theRosyProject/PIONEER/docs/manual/esp8266/adafruit_products_Huzzah_ESP8266_Pinout_v1.2-1.png.pdf

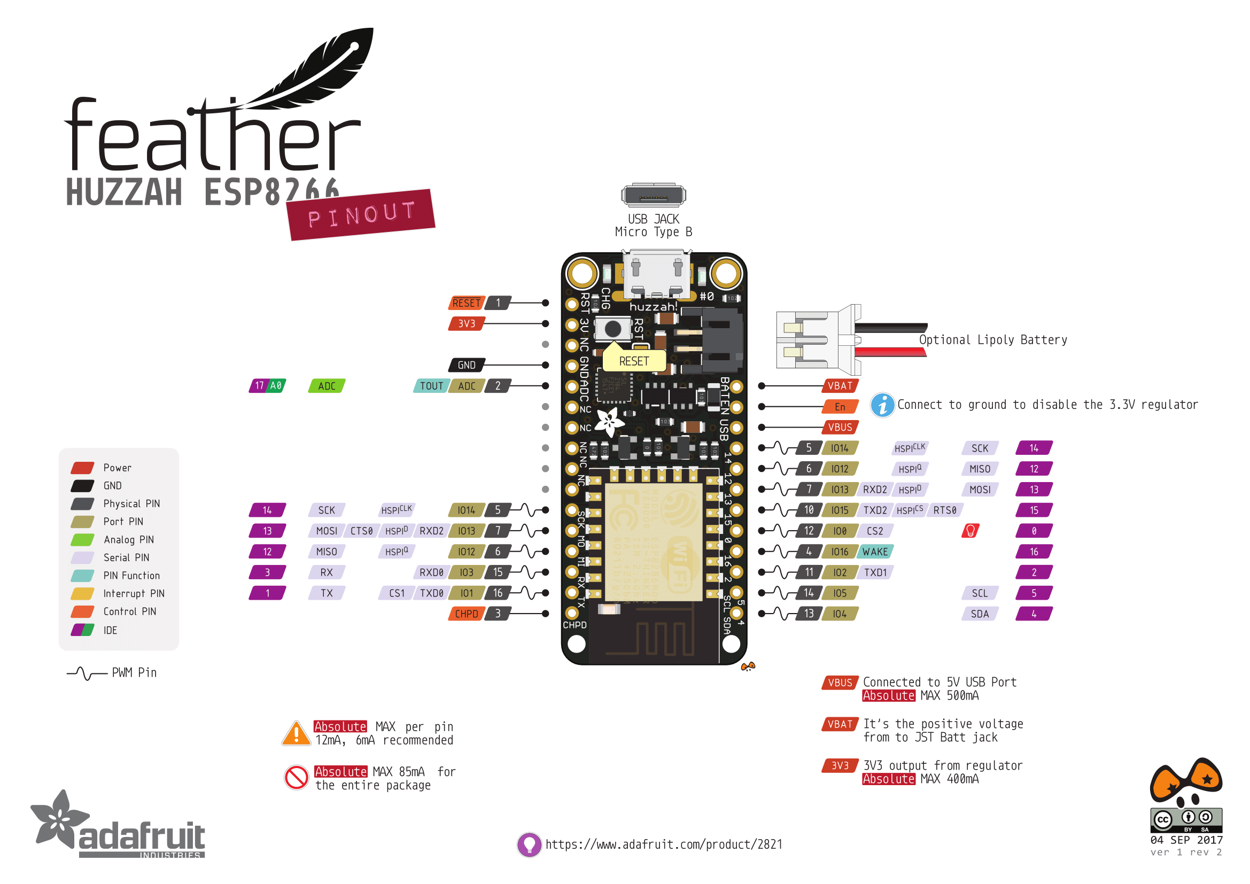
[picture p1: page 1]
