theRosyProject/PIONEER/docs/admin/meetings/2023-04-20/Screenshot 2023-04-20 at 15.48.45.png

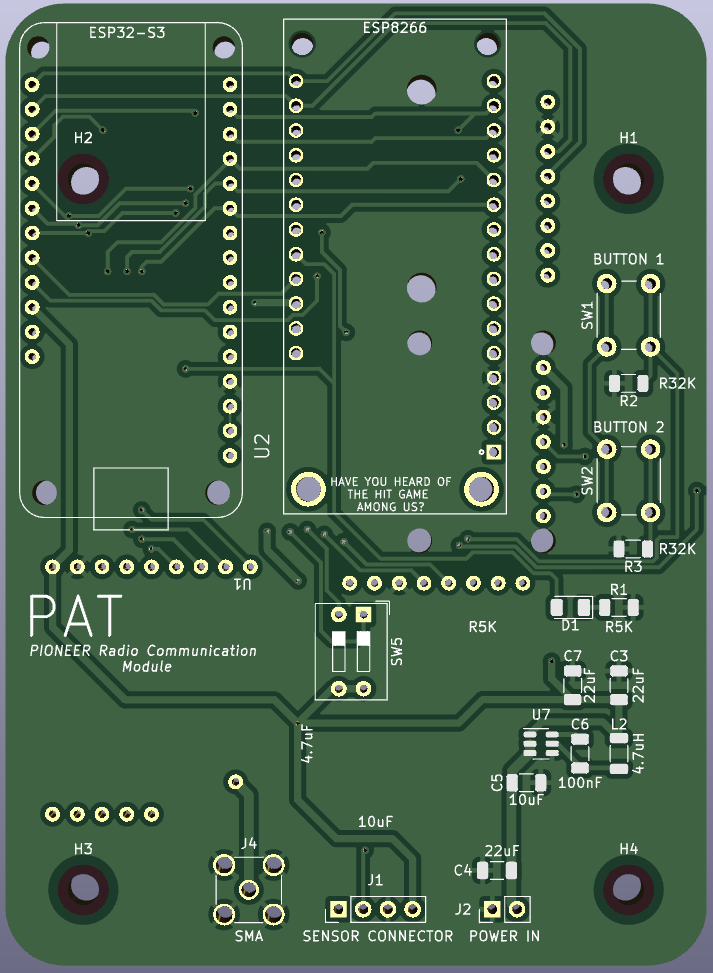
docs/admin/meetings/2023-04-20/Screenshot 2023-04-20 at 15.48.45.png
