theRosyProject/PIONEER/hardware/Sensor Box/Sensors/NDIR Transmitter.SLDPRT

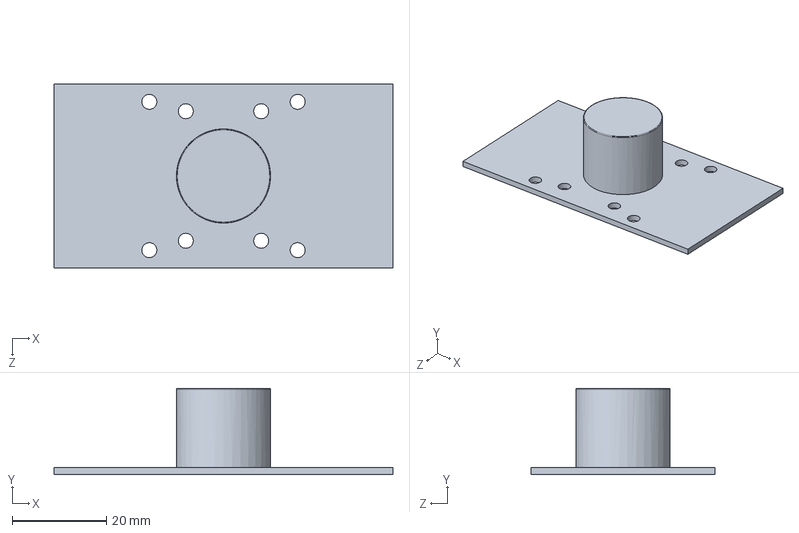
[picture p21: CAD file, 2023-03-03]
hardware/Sensor Box/Sensors/NDIR Transmitter.SLDPRT
72.0 x 18.3 x 39.0 mm
