theRosyProject/PIONEER/hardware/Controller Box/Box/Box_Lid.SLDPRT

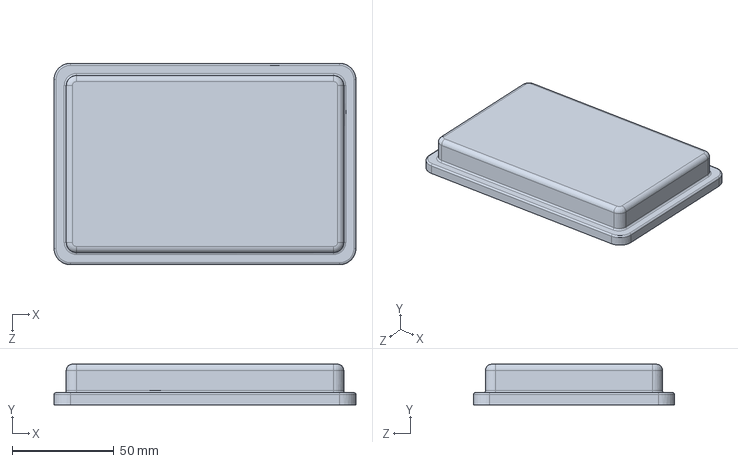
[picture p22: CAD file, 2022-10-02]
hardware/Controller Box/Box/Box_Lid.SLDPRT
148.5 x 20.0 x 99.0 mm
