theRosyProject/PIONEER/hardware/Controller Box/PCB Models/PCB_Board.SLDPRT

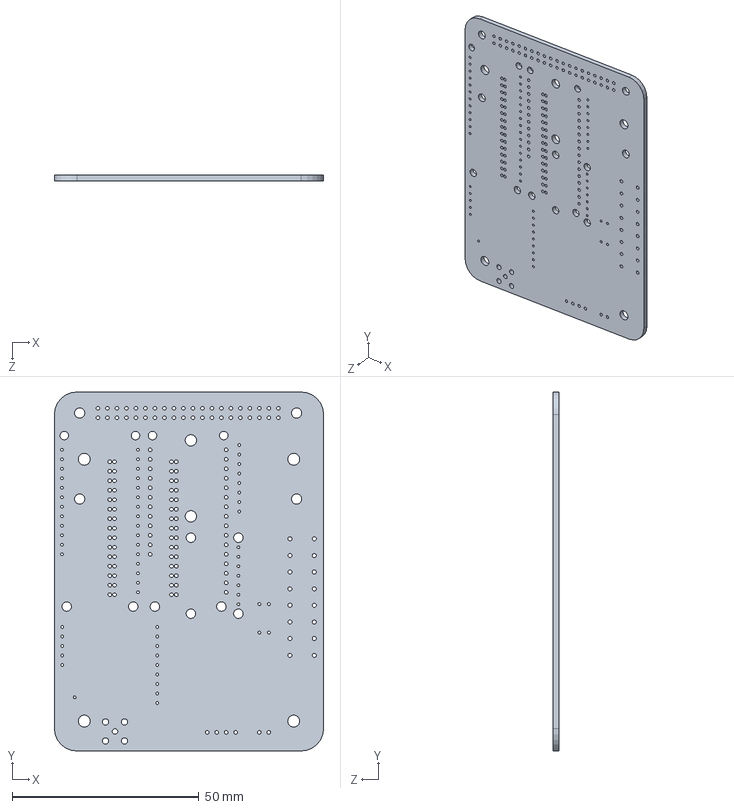
[picture p24: CAD file, 2022-10-10]
hardware/Controller Box/PCB Models/PCB_Board.SLDPRT
72.0 x 96.0 x 1.60 mm
