theRosyProject/PIONEER/hardware/Controller Box/PCB Models/stp/SW-NDS-02V.stp

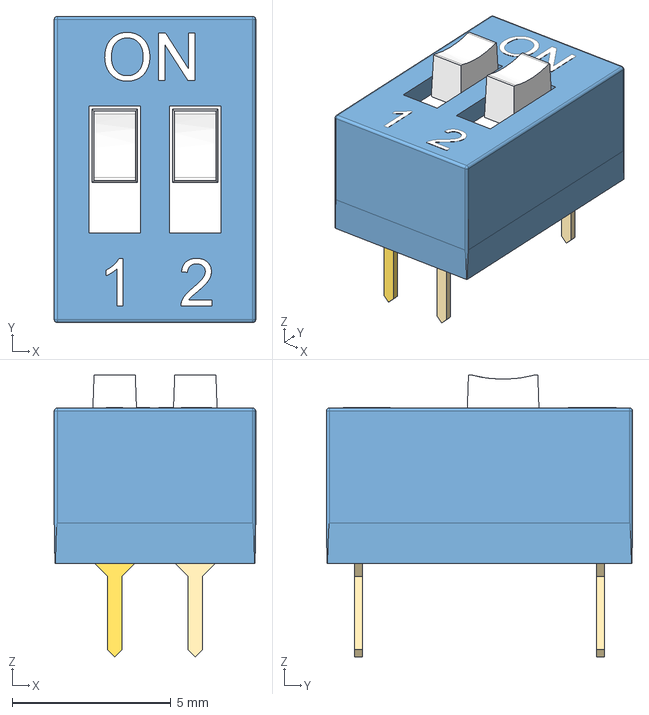
[picture p25: CAD file, 2022-10-10]
hardware/Controller Box/PCB Models/stp/SW-NDS-02V.stp
6.35 x 9.65 x 8.88 mm
