theRosyProject/PIONEER/hardware/Controller Box/PCB_Simplified.SLDPRT

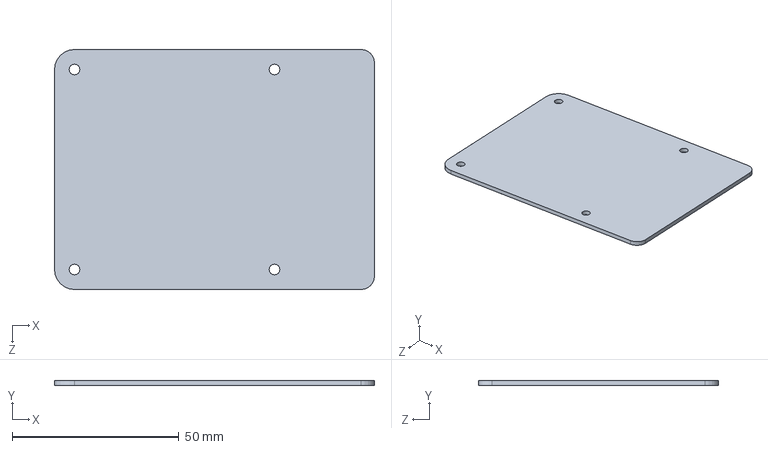
[picture p26: CAD file, 2022-10-02]
hardware/Controller Box/PCB_Simplified.SLDPRT
96.0 x 1.60 x 72.0 mm
