theRosyProject/PIONEER/hardware/Sensor Box/Sensors/PMS5003.SLDPRT

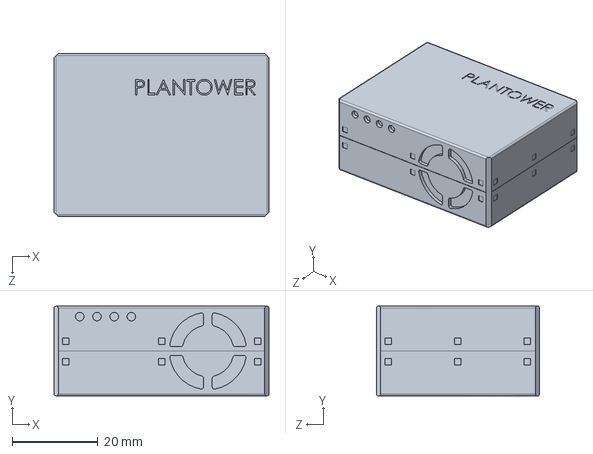
[picture p27: CAD file, 2022-11-28]
hardware/Sensor Box/Sensors/PMS5003.SLDPRT
50.0 x 20.9 x 38.0 mm
