theRosyProject/PIONEER/hardware/Controller Box/Connectors/Connector Cnlinko LP-12 2 poles.STEP

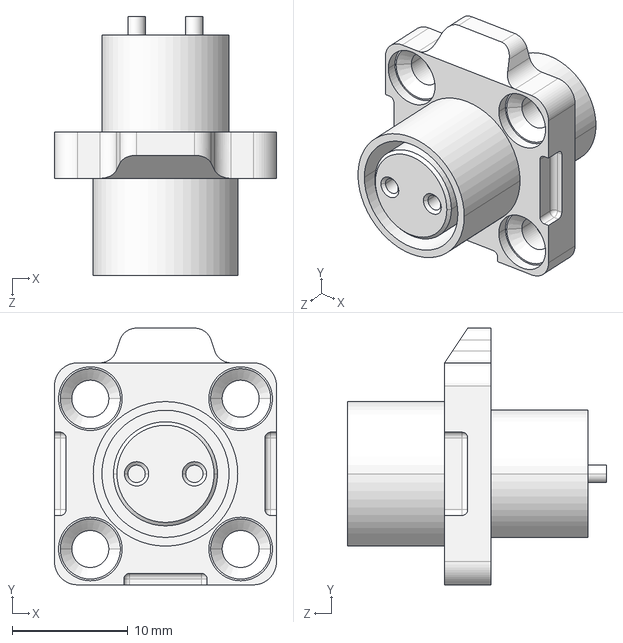
[picture p28: CAD file, 2022-10-08]
hardware/Controller Box/Connectors/Connector Cnlinko LP-12 2 poles.STEP
19.2 x 22.2 x 22.4 mm
