theRosyProject/PIONEER/hardware/Controller Box/PCB Models/stp/SW-NDS-08V.stp

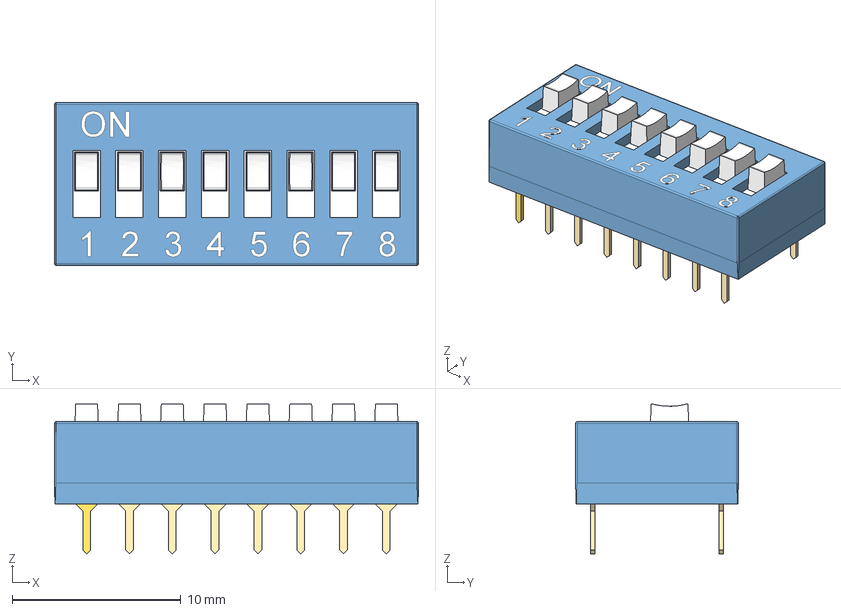
[picture p30: CAD file, 2022-10-10]
hardware/Controller Box/PCB Models/stp/SW-NDS-08V.stp
21.6 x 9.65 x 8.88 mm
