theRosyProject/PIONEER/hardware/Sensor Box/Sensors/Alphsense_Gas_Sensor.SLDPRT

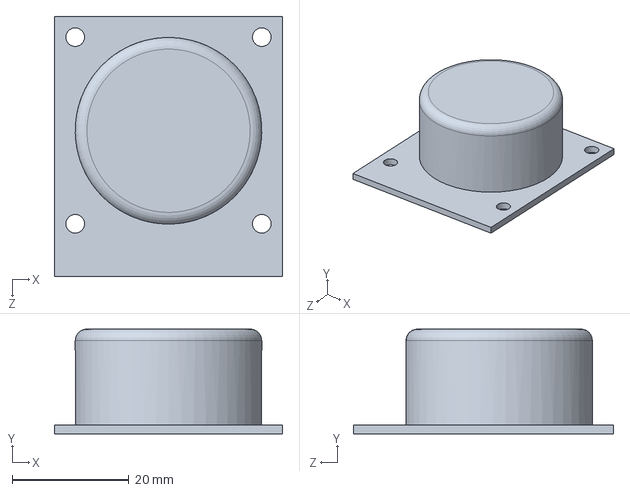
[picture p31: CAD file, 2022-11-28]
hardware/Sensor Box/Sensors/Alphsense_Gas_Sensor.SLDPRT
39.1 x 18.0 x 44.6 mm
