theRosyProject/PIONEER/hardware/Controller Box/PCB Models/stp/SW-NDS-04V.stp

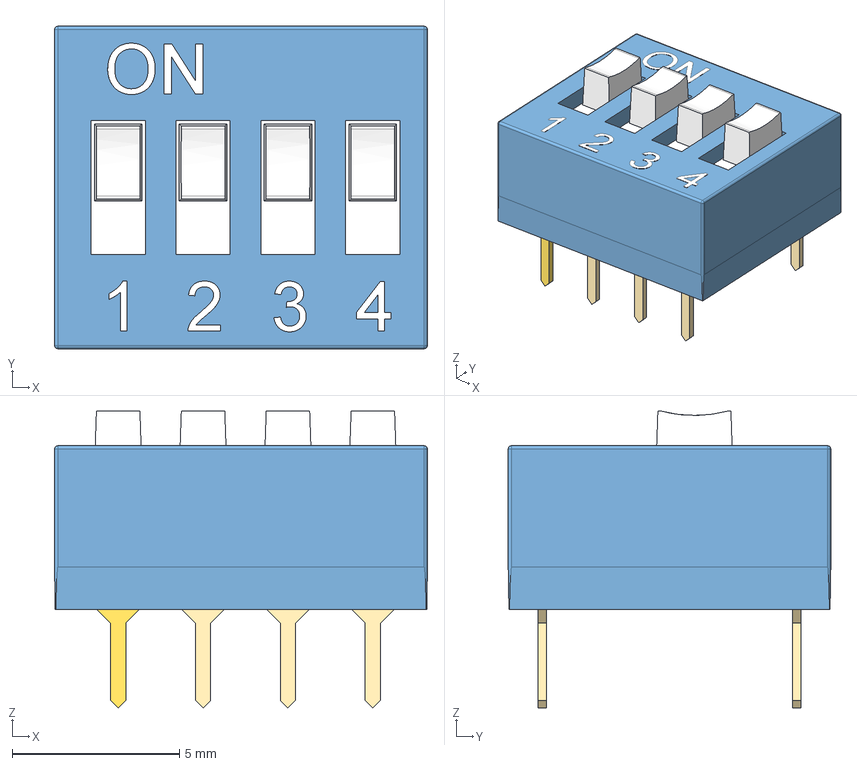
[picture p33: CAD file, 2022-10-10]
hardware/Controller Box/PCB Models/stp/SW-NDS-04V.stp
11.2 x 9.65 x 8.88 mm
