theRosyProject/PIONEER/hardware/STL Files/top_frame.STL

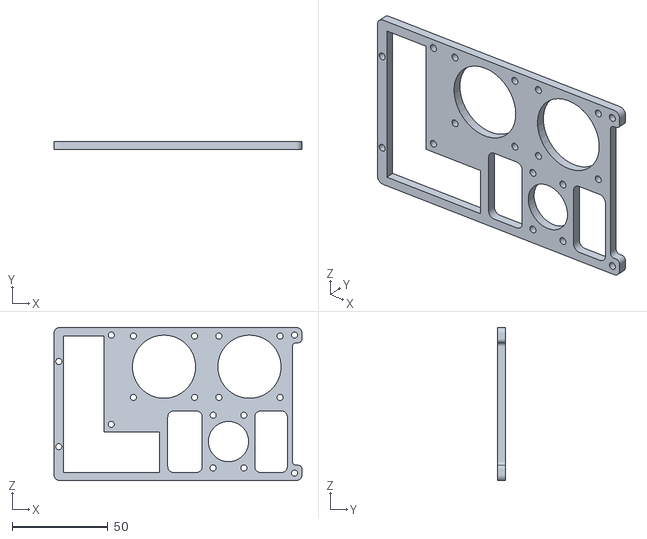
[picture p34: CAD file, 2023-03-03]
hardware/STL Files/top_frame.STL
129.4 x 4.00 x 79.9
