theRosyProject/PIONEER/hardware/Controller Box/PCB Models/stp/SW-NDS-06V.stp

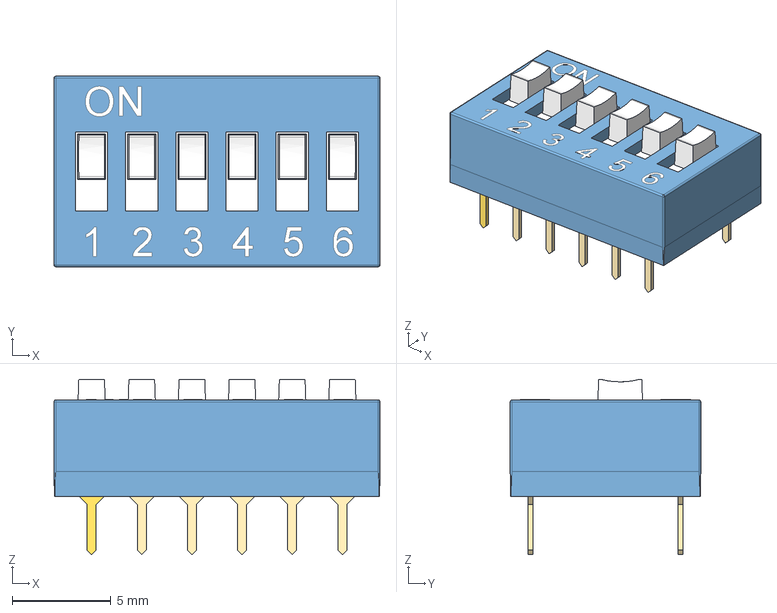
[picture p36: CAD file, 2022-10-10]
hardware/Controller Box/PCB Models/stp/SW-NDS-06V.stp
16.5 x 9.65 x 8.88 mm
