theRosyProject/PIONEER/hardware/Controller Box/PCB Models/Tactal Switch - SMD (12mmx12mmx5.5mm).stp

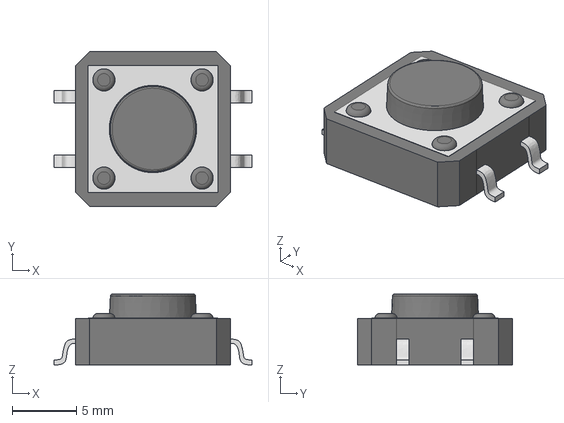
[picture p37: CAD file, 2022-10-08]
hardware/Controller Box/PCB Models/Tactal Switch - SMD (12mmx12mmx5.5mm).stp
15.4 x 12.0 x 5.50 mm
