theRosyProject/PIONEER/hardware/Controller Box/PCB Models/stp/SW-NDS-07V.stp

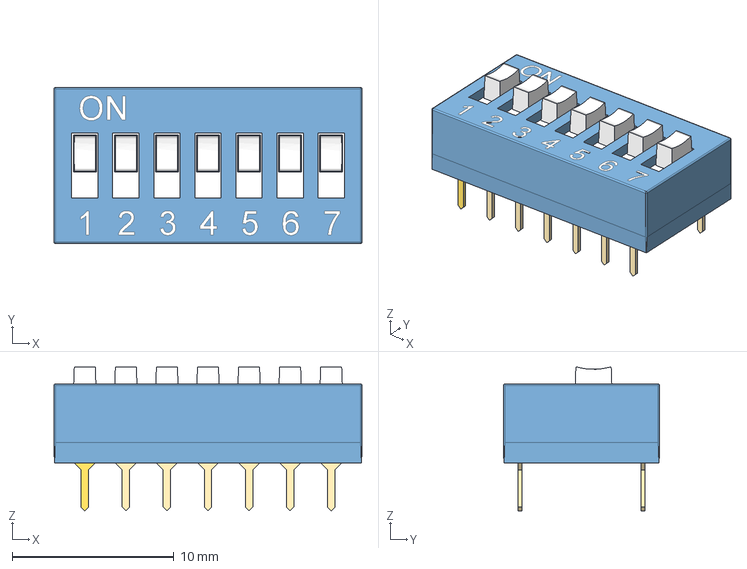
[picture p39: CAD file, 2022-10-10]
hardware/Controller Box/PCB Models/stp/SW-NDS-07V.stp
19.1 x 9.65 x 8.88 mm
