theRosyProject/PIONEER/hardware/Controller Box/PCB Models/Tactal Switch -Thru (6mmx 6mmx4.5mm).stp

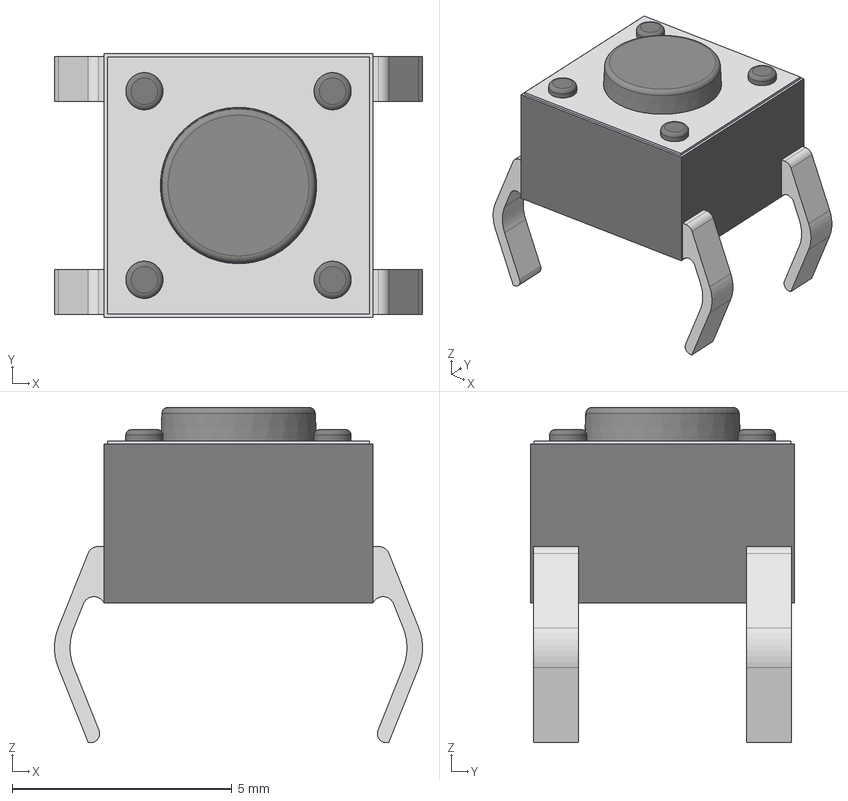
[picture p40: CAD file, 2022-10-08]
hardware/Controller Box/PCB Models/Tactal Switch -Thru (6mmx 6mmx4.5mm).stp
8.37 x 5.99 x 7.62 mm
