theRosyProject/PIONEER/hardware/Sensor Box/Sensor_PCB.SLDPRT

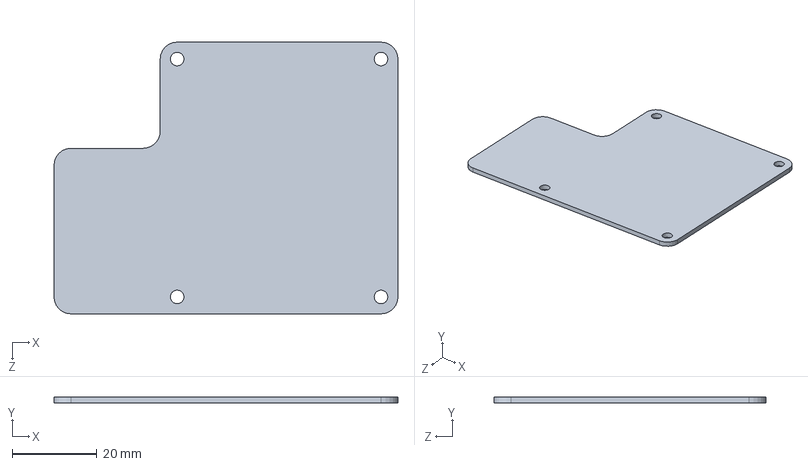
[picture p41: CAD file, 2023-01-13]
hardware/Sensor Box/Sensor_PCB.SLDPRT
81.0 x 1.50 x 64.0 mm
