theRosyProject/PIONEER/hardware/Controller Box/PCB Models/stp/SW-NDS-03V.stp

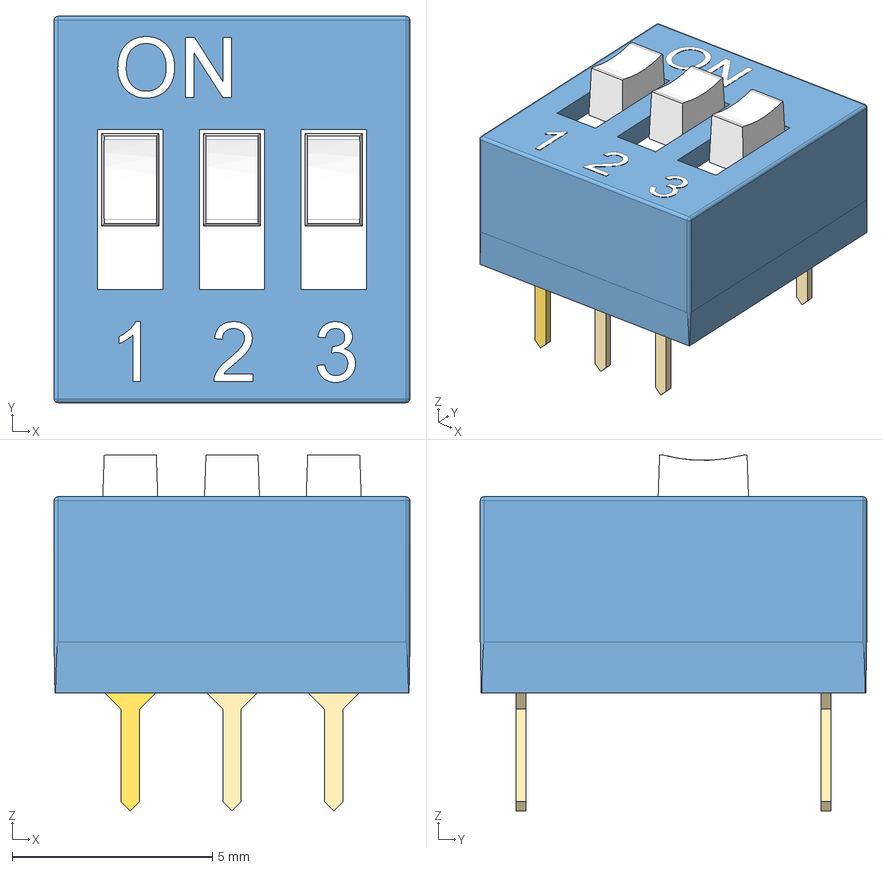
[picture p43: CAD file, 2022-10-10]
hardware/Controller Box/PCB Models/stp/SW-NDS-03V.stp
8.89 x 9.65 x 8.88 mm
