theRosyProject/PIONEER/hardware/Controller Box/PCB Models/female_header_pins/3-Pin Header - Female - 2.54mm.step

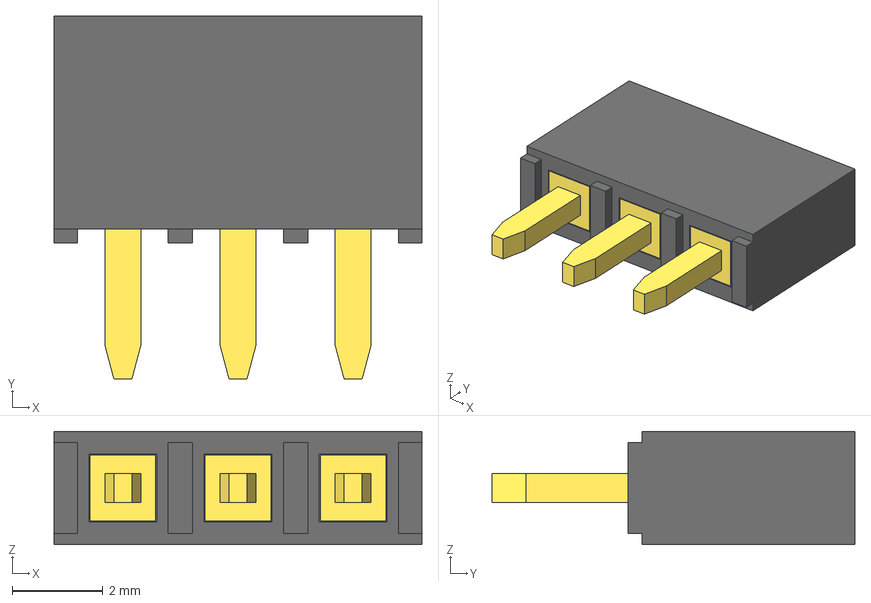
[picture p44: CAD file, 2022-10-08]
hardware/Controller Box/PCB Models/female_header_pins/3-Pin Header - Female - 2.54mm.step
8.12 x 8.00 x 2.50 mm
