theRosyProject/PIONEER/hardware/Controller Box/PCB Models/stp/SW-NDS-05V.stp

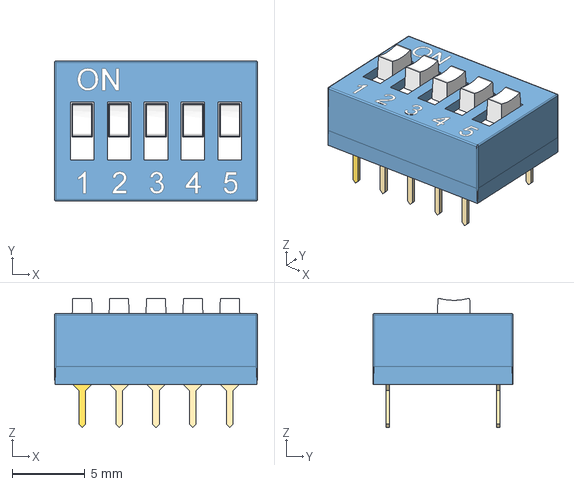
[picture p45: CAD file, 2022-10-10]
hardware/Controller Box/PCB Models/stp/SW-NDS-05V.stp
14.0 x 9.65 x 8.88 mm
