theRosyProject/PIONEER/hardware/Controller Box/PCB Models/stp/SW-NDS-10V.stp

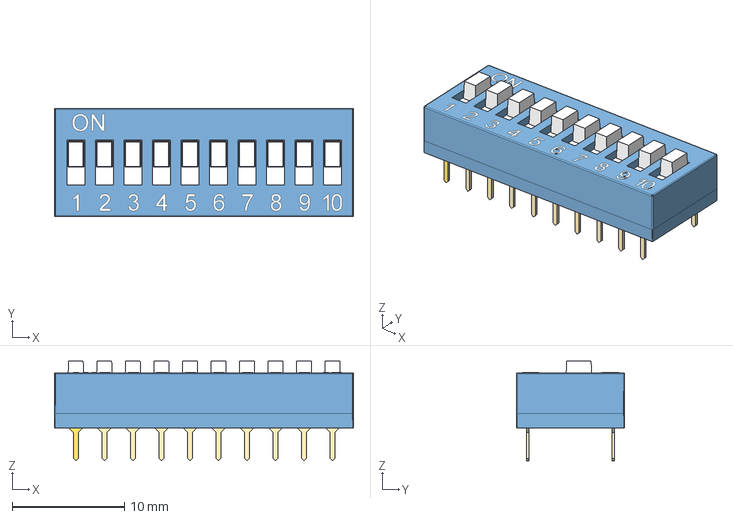
[picture p47: CAD file, 2022-10-10]
hardware/Controller Box/PCB Models/stp/SW-NDS-10V.stp
26.6 x 9.65 x 8.88 mm
