theRosyProject/PIONEER/hardware/Controller Box/PCB Models/female_header_pins/7-Pin Header - Female - 2.54mm.step

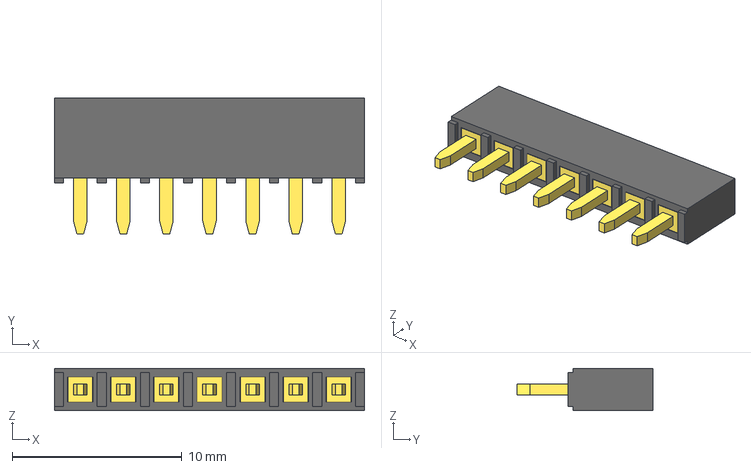
[picture p57: CAD file, 2022-10-08]
hardware/Controller Box/PCB Models/female_header_pins/7-Pin Header - Female - 2.54mm.step
18.3 x 8.00 x 2.50 mm
