theRosyProject/PIONEER/hardware/Controller Box/PCB Models/female_header_pins/13-Pin Header - Female - 2.54mm.step

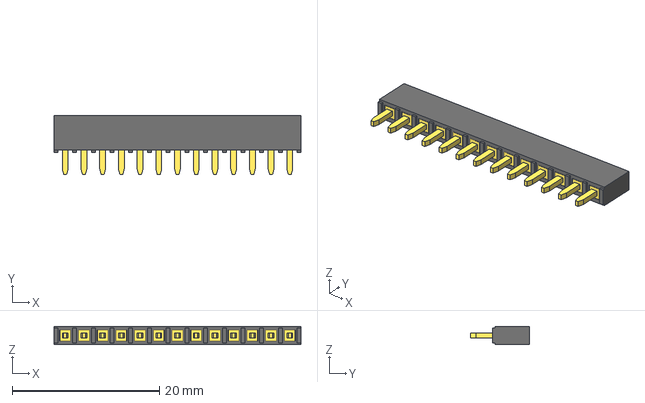
[picture p58: CAD file, 2022-10-08]
hardware/Controller Box/PCB Models/female_header_pins/13-Pin Header - Female - 2.54mm.step
33.5 x 8.00 x 2.50 mm
