theRosyProject/PIONEER/docs/manual/plantower/PMS5003-Informational.pdf

PMS5003 Particulate Sensor

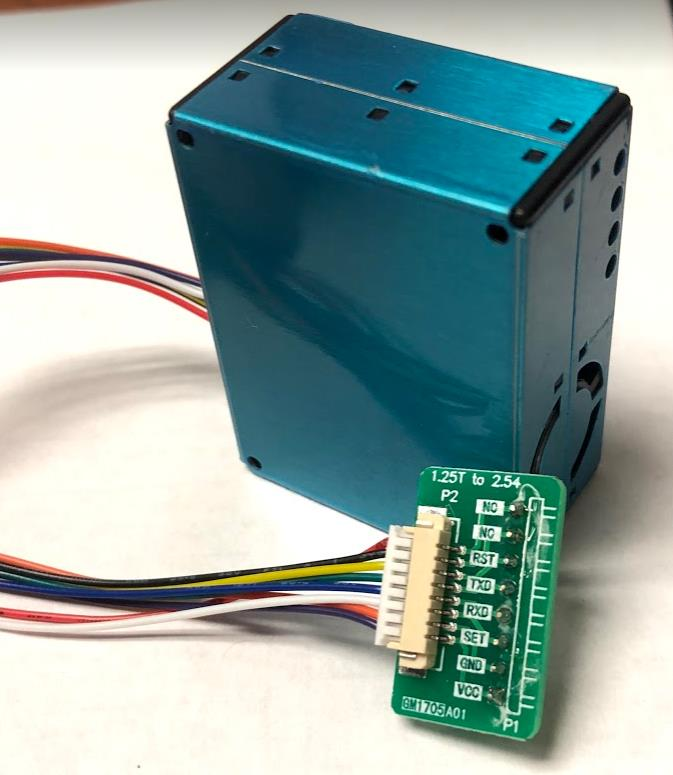
[picture p59: figure]

The PMS5003 particulate sensor is a laser scattering sensor that gives digital outputs of the concentration of suspended particles in the air. It can detect a particle diameter down to 0.3 µm. Other characteristics that make the PMS5003 desirable include the real-time responses, high anti-interference performance, and optional direction of air inlet and outlet flow.¹
This
walkthrough will describe how the sensor functions and how to set up the sensor for use on a Raspberry Pi.

How does the PMS5003 work?

Figure 1: PMS5003 Sensor

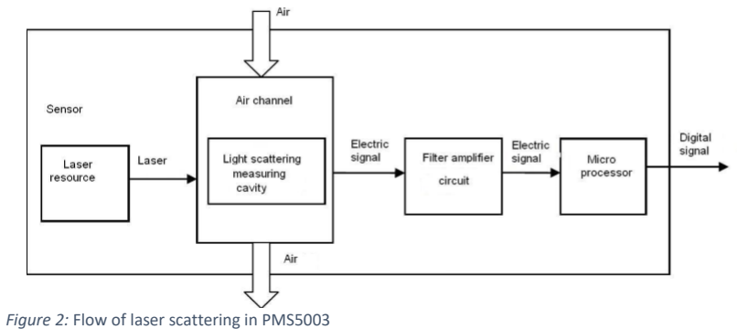
[picture p60: figure]

Figure 2: Flow of laser scattering in PMS5003

This sensor analyzes duct particles with the use of laser scattering. Laser scattering radiates light off the particles in the air and obtains the scattering pattern of the emitted light.¹ The emitted light can travel in multiple directions (forwards, backwards, up, down, left, and right) depending on the size of the particle irradiated. These “patterns” are referred to as the light intensity distribution pattern.²
Following figure 2 above, the sensor emits a laser into the cavity in which a fan blows surrounding air threw. The scattered light from the particles is converted into an electrical signal. This signal is then sent to an amplifier to enhance the signal for processing using the MIE theory in the microprocessor. The digital output is then given in units of diameter / unit volume.

1
MIE theory is the solution of the Maxwell equations for the scattering of electromagnetic waves on spherical particles. A few notes about the MIE theory: “particles are opaque discs, light is scattered at narrow angles, all particles have the same efficiency when scattering light, and the refractive index difference between the particle and surrounding medium is infinite.”³ The PMS5003 digital output has two optional modes. The default mode is the active mode. This mode sends the serial data automatically. If there are no changes in the particle concentration the active mode reads every 2.3 seconds. Once a substantial change in concentration has been detected a fast mode is activated and the sensor will read every 200~800 milliseconds.¹

Connected the PMS5003

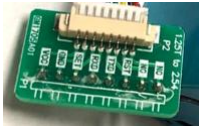
[picture p61: figure]

The PMS5003 unit comes with a board that allows for easy attachment to the raspberry pi breadboard. Very little wiring is needed to connect the PMS5003 to the pi unit. It
communicates through the serial port utilizing the TXD and RXD ports on the cobbler. Once the unit is attached to the supplied board and the board is connected to the breadboard, connect the unit to the raspberry pi as follows:

Connect Pi 5.0V to PMS VOU.
Connect Pi GND to PMS GND. Connect Pi TXD to PMS5003 RXD.
Connect Pi RXD to PMS5003 TXD.

After the everything is connected, the serial port needs to be enabled. This is done from the command line on the raspberry pi as follows:

Enter sudo raspi-config into command line

Figure 3: Connecting board for the PMS5003

Go to the interfacing option and select serial
Disable the serial login shell and enable the serial port

Now the sensor is ready for analysis.

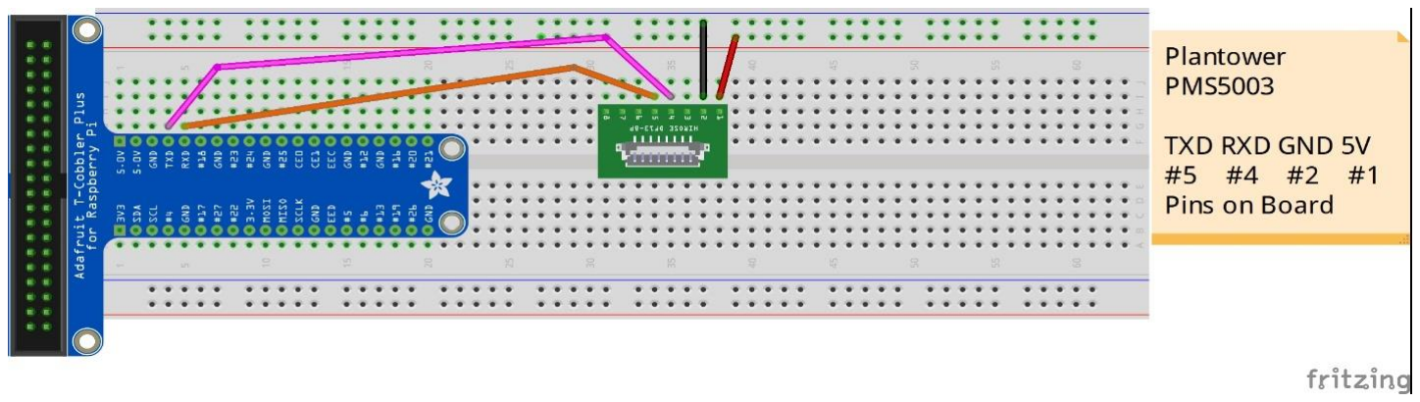
[picture p62: figure]

Figure 4: Connecting PMS5003

Coding the PMS5003

Coding for this sensor is based off the active mode that starts once the sensor is powered. If using a Raspberry Pi 3, note that the serial port is now /dev/ttyS0.⁴

These are the libraries needed to run the PMS5003 and to calculate the concentrations of the particles’ sizes. (These libraries should already be installed on Raspberry Pi when purchased). In order to obtain the digital output values, the port location is set up in the code. As mentioned above, the serial port is /dev/ttyS0 for a raspberry pi 3. From the data sheet, the baudrate is set to 9600 bps.

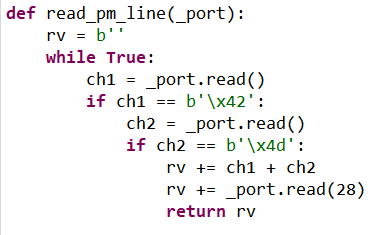
[picture p63: figure]

This part of the codes makes sure the start characters 1 and 2 are reading correctly in the serial port. Character 1 (ch1) is fixed at 0x42 and character 2 (ch2) is fixed at 0x4d. These start characters ensure that the data is being read properly from the serial port, they correlate with the hexadecimal values the pi is reading as data.

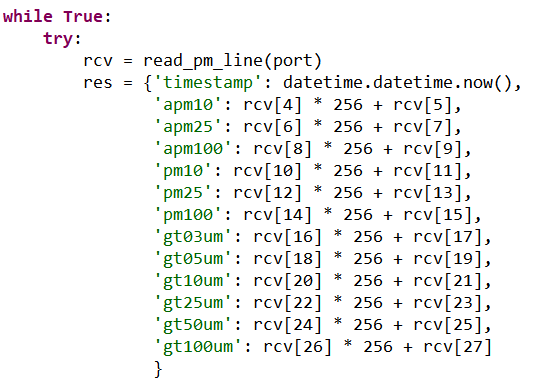
[picture p64: figure]

This part of the code is taking each piece of the serial stream (16 byte stream) and converting it from the hexadecimal values to the output values. The apm10, 25, and 100 are the factory calibration settings. PM10, 25, and 100 are the generic atmospheric conditions for calibration. The gt03, 05, 10, 25, 50, 100 are the number of particles with certain diameter readings. (all units are unit ug/m³
). The rcv values are the high and low bit values obtained from the serial port. The [#] are the corresponding placement in the data stream. The first high 8 bit reading is multiplied by 256 to shift the bit value over by 8 places to the left in order to add it to the lower 8 bit value reading. This is also the same as << 8.

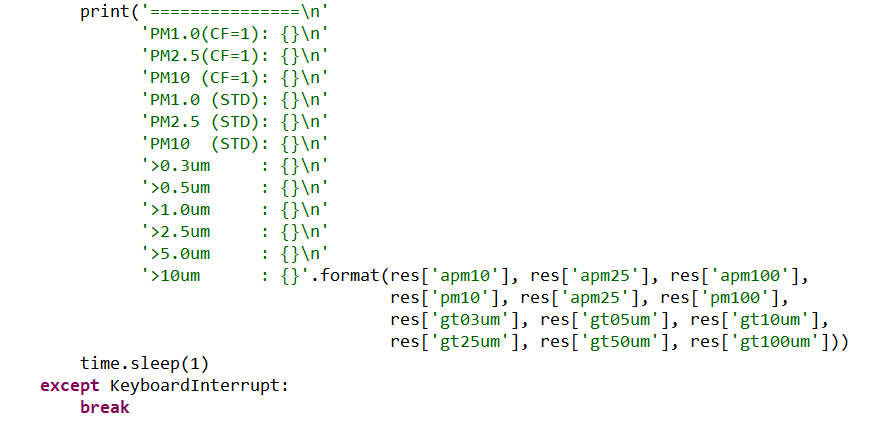
[picture p65: figure]

The rest of the code simply prints the values obtained above with the correct units, units g/m³ in
0.1 L air. The sensor will also loop every second.

References

(1) plantower-pms5003-manual_v2-3.pdf, https://cdn-shop.adafruit.com/product-files/3686/plantower-pms5003-manual_v2-3.pdf, (accessed Feb 15, 2009).
(2) Particle Size Distribution Measurement by the Laser Diffraction/Scattering Method Part1 : SHIMADZU (Shimadzu Corporation) https://www.shimadzu.com/an/powder/support/middle/m01.html (accessed Feb 15, 2019).
(3) Mie-Theory-the-first-hundred-years-MRK1304-02.pdf, https://www.atascientific.com.au/wp-content/uploads/2017/02/Mie-Theory-the-first-hundred-years-MRK1304-02.pdf, (accessed Feb 15, 2019).
(4) 262588213843476. Raspberry Pi and PMS5003 https://gist.github.com/lackofdream/bc8649d647240ef14311 (accessed Feb 15, 2019).
